istratoudakis/All-in-one_Controller/Version_4_All-in-one_Controller/src/discord_handler_keys.py

import keyboard

def handle_discord_shortcuts(command):
    if command == "DISCORD_MUTE":
        keyboard.send("ctrl+shift+m")
    elif command == "DISCORD_DEAFEN":
        keyboard.send("ctrl+shift+d")
